eriklovekin/fimur/assets/img/allan/20260712-225526/allan_accel1_lib.png

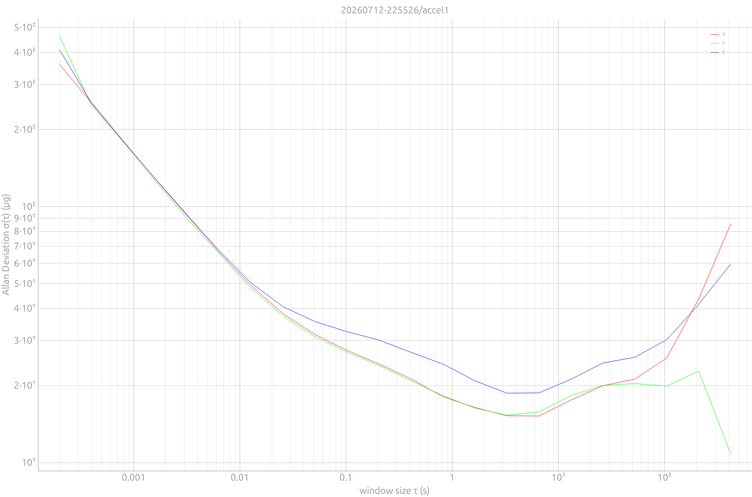
assets/img/allan/20260712-225526/allan_accel1_lib.png
