eriklovekin/fimur/assets/img/allan/20260712-225526/allan_gyro1.png

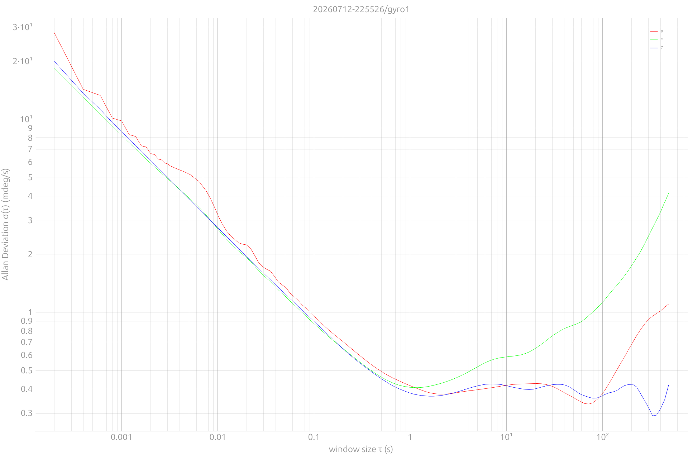
assets/img/allan/20260712-225526/allan_gyro1.png
