eriklovekin/fimur/assets/img/allan/20260712-225526/allan_gyro2.png

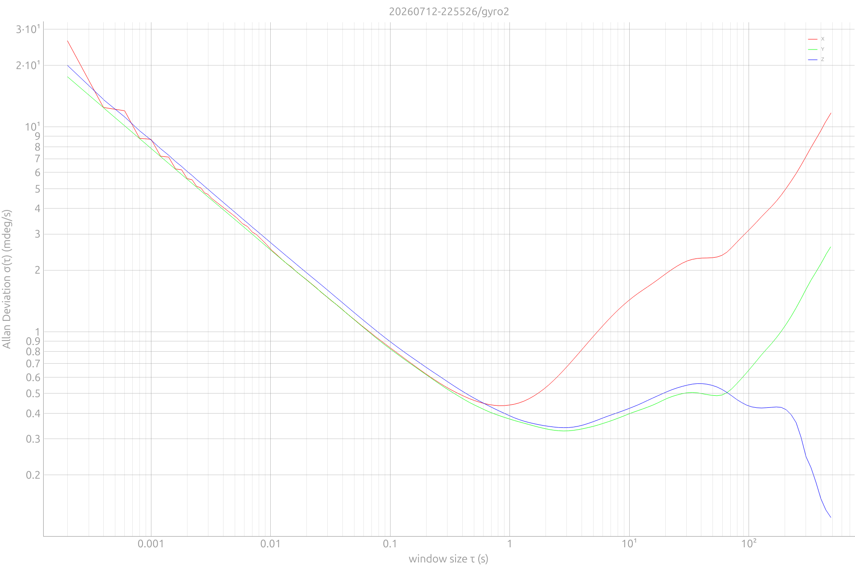
assets/img/allan/20260712-225526/allan_gyro2.png
