eriklovekin/fimur/assets/img/allan/20260712-225526/allan_gyro2_lib.png

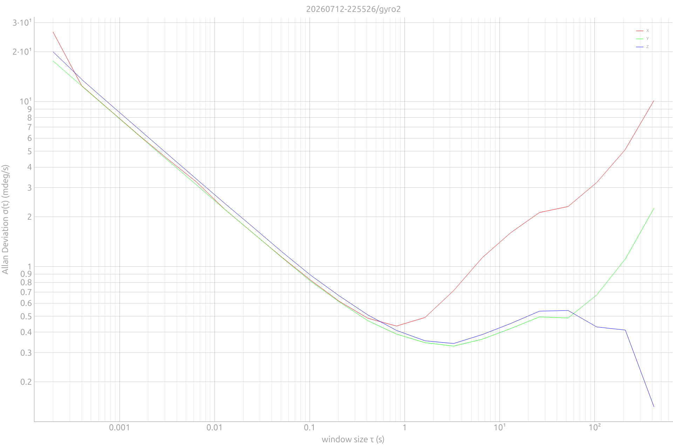
assets/img/allan/20260712-225526/allan_gyro2_lib.png
