eriklovekin/fimur/assets/img/allan/20260725-233150/allan_accel1.png

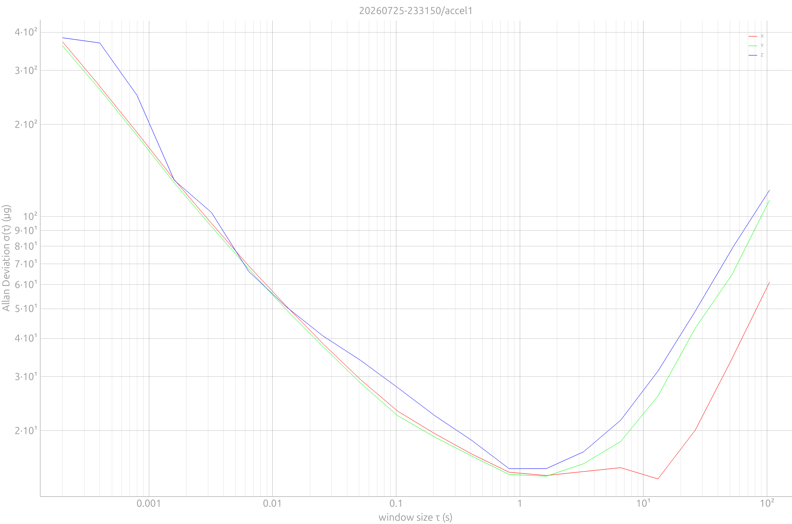
assets/img/allan/20260725-233150/allan_accel1.png
