eriklovekin/fimur/assets/img/allan/20260725-233150/allan_accel9.png

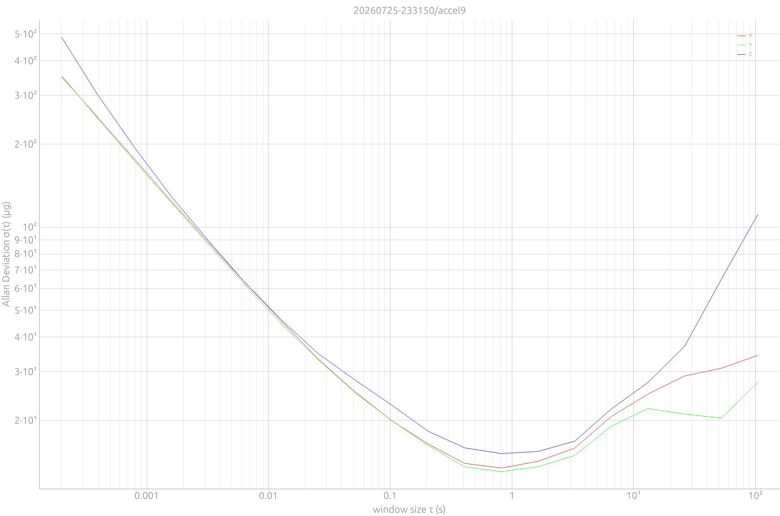
assets/img/allan/20260725-233150/allan_accel9.png
