eriklovekin/fimur/assets/img/allan/20260725-233150/allan_gyro6.png

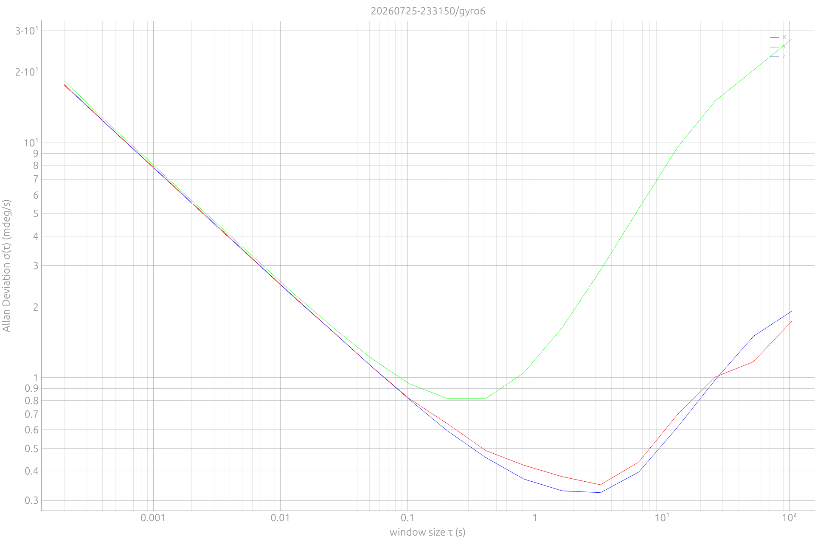
assets/img/allan/20260725-233150/allan_gyro6.png
