eriklovekin/fimur/assets/img/sensor-positions.png

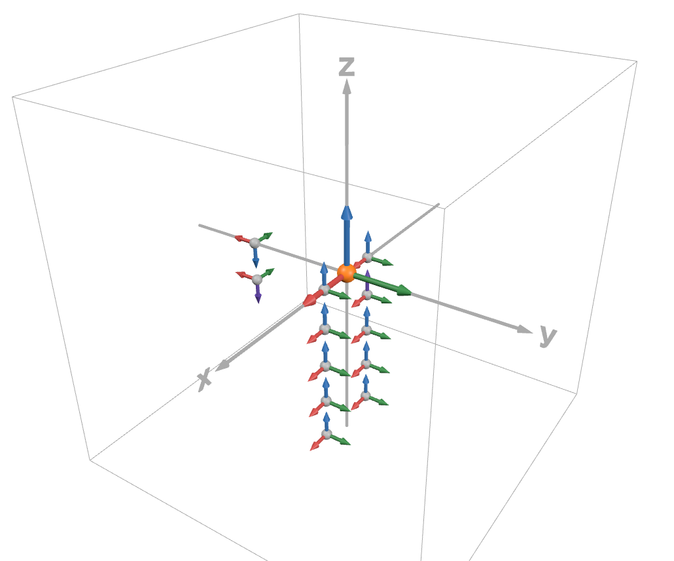
assets/img/sensor-positions.png
